Iam-Madman/dfrobot-multigas-transmitter/fabrication/stm32c0_pcb(phase2)/stm32c0_pcb(phase2).kicad_pcb

## KiCad design hardware/KiCad/SmartAlarmClock_discrete/SmartAlarmClock_discrete.kicad_sch

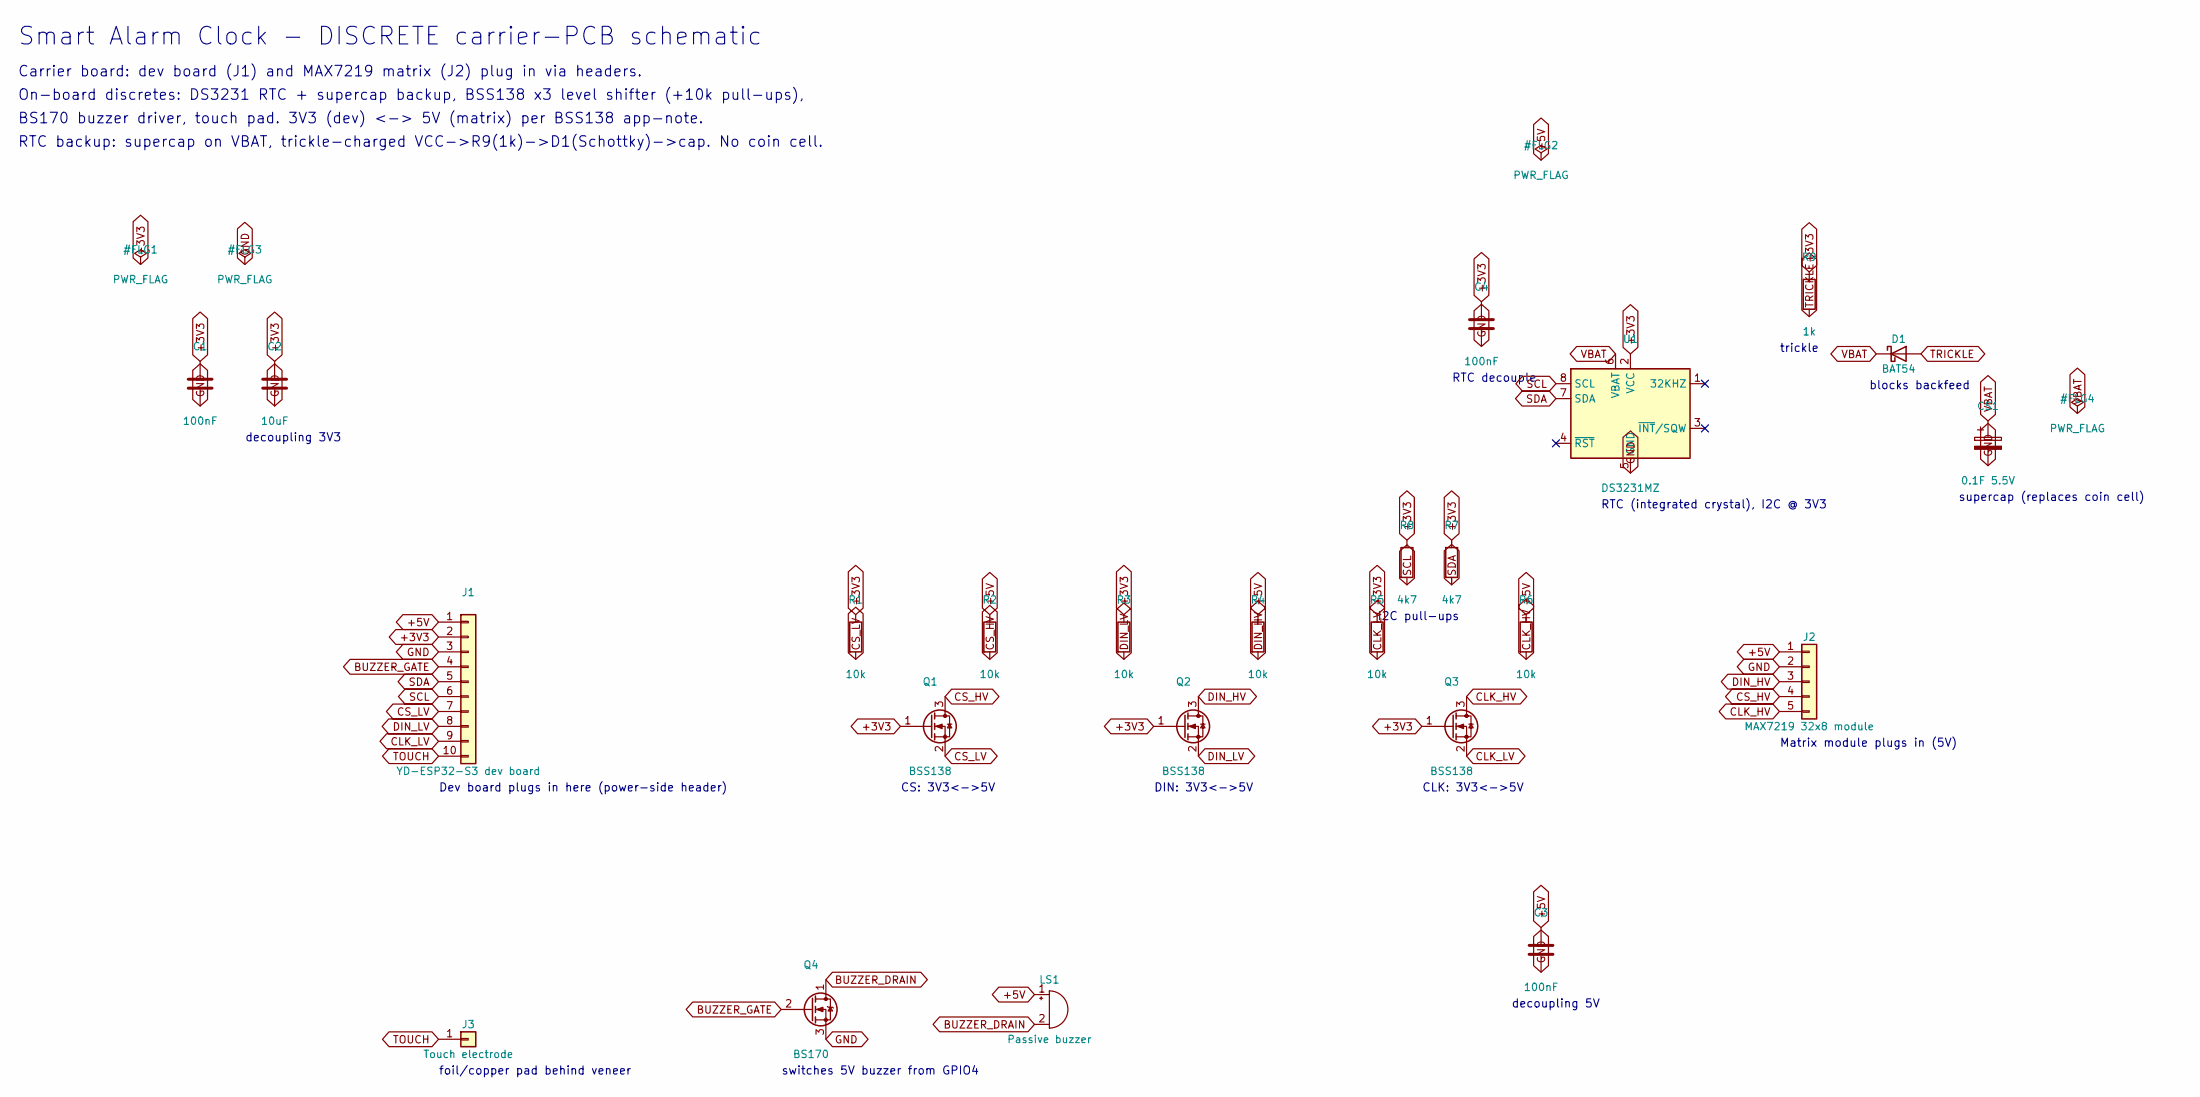
[picture p4: schematic SmartAlarmClock_discrete.kicad_sch]

Parts:
C1, C3, C4: 100nF
C2: 10uF
CS1: 0.1F 5.5V
D1: BAT54
J1: YD-ESP32-S3 dev board
J2: MAX7219 32x8 module
J3: Touch electrode
LS1: Passive buzzer
Q1, Q2, Q3: BSS138
Q4: BS170
R1, R2, R3, R4, R5, R6: 10k
R7, R8: 4k7
R9: 1k
U1: DS3231MZ

Connections:
+3V3: C1.1, C2.1, C4.1, J1.2, Q1.1 (G), Q2.1 (G), Q3.1 (G), R1.1, R3.1, R5.1, R7.1, R8.1, R9.1, U1.2 (VCC)
+5V: C3.1, J1.1, J2.1, LS1.1 (+), R2.1, R4.1, R6.1
BUZZER_DRAIN: LS1.2 (-), Q4.1 (D)
BUZZER_GATE: J1.4, Q4.2 (G)
CLK_HV: J2.5, Q3.3 (D), R6.2
CLK_LV: J1.9, Q3.2 (S), R5.2
CS_HV: J2.4, Q1.3 (D), R2.2
CS_LV: J1.7, Q1.2 (S), R1.2
DIN_HV: J2.3, Q2.3 (D), R4.2
DIN_LV: J1.8, Q2.2 (S), R3.2
GND: C1.2, C2.2, C3.2, C4.2, CS1.2, J1.3, J2.2, Q4.3 (S), U1.5 (GND)
SCL: J1.6, R8.2, U1.8 (SCL)
SDA: J1.5, R7.2, U1.7 (SDA)
TOUCH: J1.10, J3.1
TRICKLE: D1.2 (A), R9.2
VBAT: CS1.1, D1.1 (K), U1.6 (VBAT)

Notes on the sheet:
Smart Alarm Clock - DISCRETE carrier-PCB schematic
Carrier board: dev board (J1) and MAX7219 matrix (J2) plug in via headers.
On-board discretes: DS3231 RTC + supercap backup, BSS138 x3 level shifter (+10k pull-ups),
BS170 buzzer driver, touch pad. 3V3 (dev) <-> 5V (matrix) per BSS138 app-note.
RTC backup: supercap on VBAT, trickle-charged VCC->R9(1k)->D1(Schottky)->cap. No coin cell.
Dev board plugs in here (power-side header)
Matrix module plugs in (5V)
foil/copper pad behind veneer
RTC (integrated crystal), I2C @ 3V3
RTC decouple
I2C pull-ups
trickle
blocks backfeed
supercap (replaces coin cell)
CS: 3V3<->5V
DIN: 3V3<->5V
CLK: 3V3<->5V
switches 5V buzzer from GPIO4
decoupling 3V3
decoupling 5V
