Iam-Madman/dfrobot-multigas-transmitter/fabrication/stm32c0_pcb(phase2)/stm32c0_pcb(phase2).kicad_pcb

## KiCad design hardware/KiCad/SmartAlarmClock_prototype/SmartAlarmClock_prototype.kicad_sch

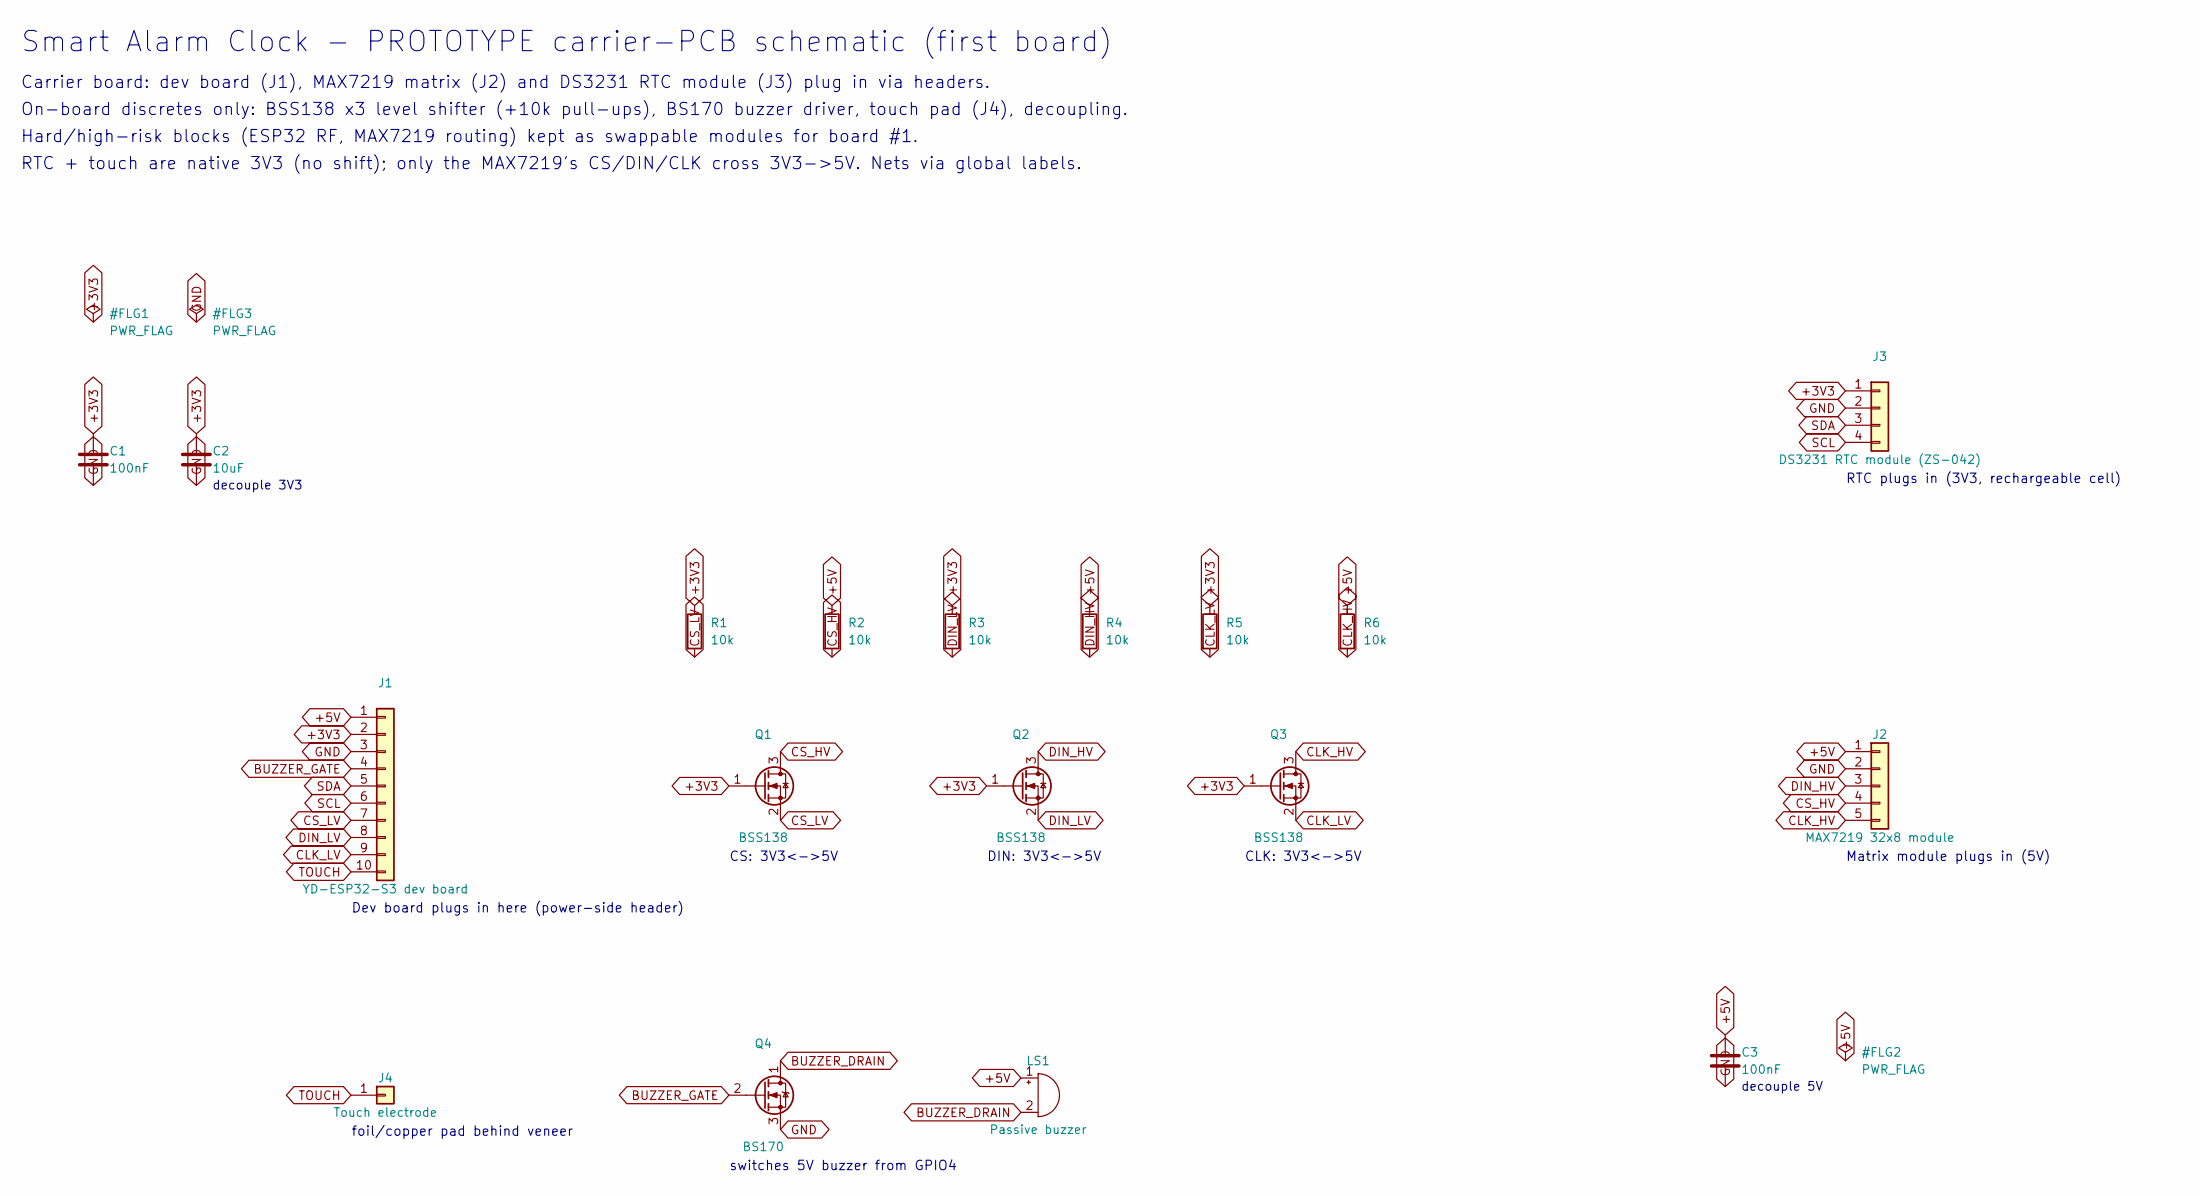
[picture p5: schematic SmartAlarmClock_prototype.kicad_sch]

Parts:
C1, C3: 100nF
C2: 10uF
J1: YD-ESP32-S3 dev board
J2: MAX7219 32x8 module
J3: DS3231 RTC module (ZS-042)
J4: Touch electrode
LS1: Passive buzzer
Q1, Q2, Q3: BSS138
Q4: BS170
R1, R2, R3, R4, R5, R6: 10k

Connections:
+3V3: C1.1, C2.1, J1.2, J3.1, Q1.1 (G), Q2.1 (G), Q3.1 (G), R1.1, R3.1, R5.1
+5V: C3.1, J1.1, J2.1, LS1.1 (+), R2.1, R4.1, R6.1
BUZZER_DRAIN: LS1.2 (-), Q4.1 (D)
BUZZER_GATE: J1.4, Q4.2 (G)
CLK_HV: J2.5, Q3.3 (D), R6.2
CLK_LV: J1.9, Q3.2 (S), R5.2
CS_HV: J2.4, Q1.3 (D), R2.2
CS_LV: J1.7, Q1.2 (S), R1.2
DIN_HV: J2.3, Q2.3 (D), R4.2
DIN_LV: J1.8, Q2.2 (S), R3.2
GND: C1.2, C2.2, C3.2, J1.3, J2.2, J3.2, Q4.3 (S)
SCL: J1.6, J3.4
SDA: J1.5, J3.3
TOUCH: J1.10, J4.1

Notes on the sheet:
Smart Alarm Clock - PROTOTYPE carrier-PCB schematic (first board)
Carrier board: dev board (J1), MAX7219 matrix (J2) and DS3231 RTC module (J3) plug in via headers.
On-board discretes only: BSS138 x3 level shifter (+10k pull-ups), BS170 buzzer driver, touch pad (J4), decoupling.
Hard/high-risk blocks (ESP32 RF, MAX7219 routing) kept as swappable modules for board #1.
RTC + touch are native 3V3 (no shift); only the MAX7219's CS/DIN/CLK cross 3V3->5V. Nets via global labels.
Dev board plugs in here (power-side header)
decouple 3V3
CS: 3V3<->5V
DIN: 3V3<->5V
CLK: 3V3<->5V
foil/copper pad behind veneer
switches 5V buzzer from GPIO4
RTC plugs in (3V3, rechargeable cell)
Matrix module plugs in (5V)
decouple 5V
